DingLongya/Awtrix/1.PCB 板子的打印 提交的Gerber/+.png

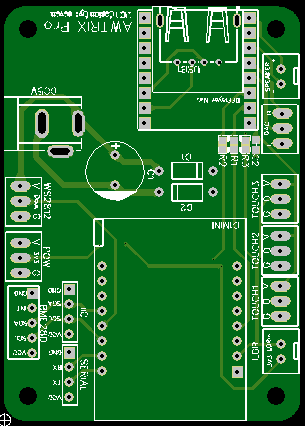
1.PCB 板子的打印 提交的Gerber/+.png
