DingLongya/Awtrix/5.3D/木板制作/格栅尺寸.jpg

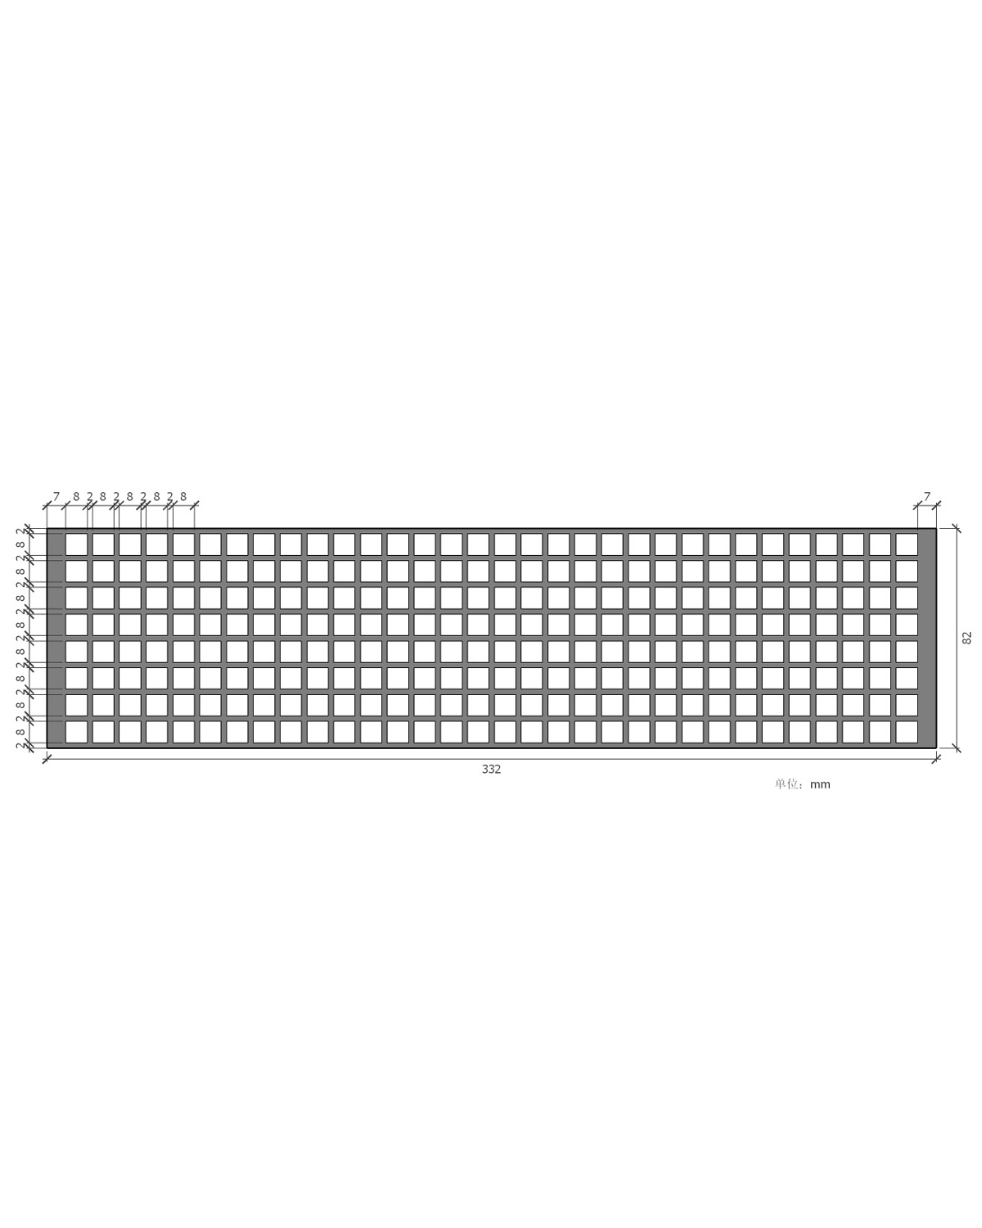
5.3D/木板制作/格栅尺寸.jpg
